Atsuko-Otsuka/PuppetManipulation/PuppetManipulation_Hardware/Arduino/9jikuGetQuaternion/9jikuGetQuaternion.ino

#include <Wire.h>
#include <Adafruit_Sensor.h>
#include <Adafruit_BNO055.h>
#include <utility/imumaths.h> 

/*
This program is an abridged version of Adafruit BNO055 rawdata.ino available after installing the Adafruit BNO055 library
File→Examples→Adafruit BNO055→Raw Data
  Connections on Arduino Uno
  =========================================================================
  SCL to analog 5 | SDA to analog 4 | VDD to 3.3V DC | GND to common ground
*/

#define BNO055_SAMPLERATE_DELAY_MS (100)          // Delay between data requests

//Adafruit_BNO055 bno = Adafruit_BNO055();          // Create sensor object bno based on Adafruit_BNO055 library
Adafruit_BNO055 bno = Adafruit_BNO055(55, 0x28);

void setup(void)
{
  Serial.begin(115200);                           // Begin serial port communication

  // Pico WのカスタムI2Cピンを設定
  Wire.setSDA(20);
  Wire.setSCL(21);

  if(!bno.begin())                                // Initialize sensor communication
  {  
    Serial.print("Ooops, no BNO055 detected ... Check your wiring or I2C ADDR!");  
  }
  delay(1000);
  bno.setExtCrystalUse(true);                     // Use the crystal on the development board
}

void loop(void)
{
  imu::Quaternion quat = bno.getQuat();           // Request quaternion data from BNO055

  Serial.print("0"); // Dummy Port Number
  Serial.print(",");
  Serial.print(quat.w(), 4); // Print quaternion w
  Serial.print(",");
  Serial.print(quat.x(), 4); // Print quaternion x
  Serial.print(",");
  Serial.print(quat.y(), 4); // Print quaternion y
  Serial.print(",");
  Serial.println(quat.z(), 4); // Print quaternion z

  delay(BNO055_SAMPLERATE_DELAY_MS);              // Pause before capturing new data
}
